noorbouharrou/CommuniMate/examples/schermen_knoppen_geluid/1.h

/* C:\Users\niels\Downloads\1.wav (03/02/2025 16:15:37)
   StartOffset(h): 00000000, EndOffset(h): 00001715, Length(h): 00001716 */

unsigned char rawData1[5910] PROGMEM = {
	0x52, 0x49, 0x46, 0x46, 0x0E, 0x17, 0x00, 0x00, 0x57, 0x41, 0x56, 0x45,
	0x66, 0x6D, 0x74, 0x20, 0x10, 0x00, 0x00, 0x00, 0x01, 0x00, 0x01, 0x00,
	0x40, 0x1F, 0x00, 0x00, 0x40, 0x1F, 0x00, 0x00, 0x01, 0x00, 0x08, 0x00,
	0x64, 0x61, 0x74, 0x61, 0x80, 0x16, 0x00, 0x00, 0x80, 0x80, 0x80, 0x80,
	0x80, 0x7F, 0x80, 0x7F, 0x80, 0x80, 0x80, 0x7F, 0x80, 0x7F, 0x80, 0x80,
	0x7F, 0x80, 0x80, 0x80, 0x80, 0x80, 0x7F, 0x80, 0x7F, 0x80, 0x7F, 0x80,
	0x7F, 0x80, 0x7F, 0x80, 0x7F, 0x7F, 0x80, 0x7F, 0x80, 0x7F, 0x80, 0x80,
	0x80, 0x7F, 0x80, 0x7F, 0x80, 0x7F, 0x80, 0x80, 0x7F, 0x80, 0x7F, 0x80,
	0x7F, 0x80, 0x80, 0x7F, 0x80, 0x7F, 0x80, 0x7F, 0x80, 0x7F, 0x80, 0x7F,
	0x80, 0x80, 0x7F, 0x80, 0x7F, 0x80, 0x80, 0x80, 0x7F, 0x80, 0x7F, 0x80,
	0x7F, 0x80, 0x7F, 0x80, 0x80, 0x7F, 0x80, 0x7F, 0x80, 0x80, 0x7F, 0x80,
	0x7F, 0x80, 0x7F, 0x80, 0x80, 0x7F, 0x80, 0x7F, 0x80, 0x7F, 0x80, 0x7F,
	0x80, 0x80, 0x7F, 0x80, 0x7F, 0x80, 0x7F, 0x80, 0x7F, 0x80, 0x80, 0x7F,
	0x80, 0x7F, 0x80, 0x80, 0x7F, 0x80, 0x7F, 0x80, 0x7F, 0x80, 0x7F, 0x80,
	0x7F, 0x80, 0x80, 0x7F, 0x80, 0x7F, 0x80, 0x7F, 0x80, 0x7F, 0x80, 0x80,
	0x7F, 0x80, 0x80, 0x80, 0x7F, 0x80, 0x7F, 0x80, 0x80, 0x80, 0x7F, 0x80,
	0x7F, 0x80, 0x7F, 0x80, 0x7F, 0x80, 0x80, 0x80, 0x7F, 0x80, 0x80, 0x7F,
	0x80, 0x7F, 0x80, 0x7F, 0x80, 0x7F, 0x80, 0x80, 0x80, 0x80, 0x80, 0x80,
	0x7F, 0x80, 0x7F, 0x80, 0x7F, 0x7F, 0x80, 0x7F, 0x80, 0x7F, 0x80, 0x7F,
	0x80, 0x80, 0x7F, 0x80, 0x7F, 0x7F, 0x80, 0x7F, 0x80, 0x80, 0x7F, 0x80,
	0x7F, 0x80, 0x7F, 0x80, 0x80, 0x7F, 0x80, 0x7F, 0x80, 0x7F, 0x80, 0x7F,
	0x80, 0x7F, 0x80, 0x7F, 0x80, 0x7F, 0x80, 0x7F, 0x80, 0x7F, 0x7F, 0x80,
	0x7F, 0x80, 0x80, 0x7F, 0x80, 0x7F, 0x80, 0x7F, 0x80, 0x80, 0x80, 0x80,
	0x80, 0x80, 0x80, 0x80, 0x80, 0x7F, 0x80, 0x7F, 0x80, 0x7F, 0x80, 0x7F,
	0x80, 0x7F, 0x80, 0x80, 0x7F, 0x80, 0x7F, 0x80, 0x7F, 0x80, 0x7F, 0x80,
	0x7F, 0x80, 0x7F, 0x80, 0x7F, 0x80, 0x7F, 0x80, 0x80, 0x7F, 0x80, 0x7F,
	0x80, 0x7F, 0x80, 0x7F, 0x80, 0x80, 0x7F, 0x80, 0x7F, 0x80, 0x7F, 0x80,
	0x80, 0x7F, 0x80, 0x7F, 0x80, 0x80, 0x80, 0x7F, 0x80, 0x80, 0x7F, 0x80,
	0x7F, 0x80, 0x7F, 0x80, 0x80, 0x7F, 0x80, 0x80, 0x7F, 0x80, 0x7F, 0x80,
	0x7F, 0x80, 0x7F, 0x80, 0x7F, 0x80, 0x7F, 0x80, 0x7F, 0x80, 0x7F, 0x80,
	0x7F, 0x80, 0x7F, 0x80, 0x7F, 0x80, 0x80, 0x7F, 0x80, 0x80, 0x7F, 0x80,
	0x7F, 0x80, 0x80, 0x7F, 0x80, 0x7F, 0x80, 0x80, 0x7F, 0x80, 0x80, 0x7F,
	0x80, 0x80, 0x7F, 0x80, 0x7F, 0x80, 0x7F, 0x80, 0x7F, 0x80, 0x7F, 0x80,
	0x7F, 0x80, 0x7F, 0x80, 0x7F, 0x80, 0x80, 0x7F, 0x80, 0x80, 0x7F, 0x80,
	0x7F, 0x7F, 0x80, 0x7F, 0x80, 0x7F, 0x80, 0x80, 0x80, 0x80, 0x80, 0x80,
	0x80, 0x80, 0x7F, 0x80, 0x80, 0x7F, 0x80, 0x80, 0x7F, 0x80, 0x7F, 0x80,
	0x7F, 0x80, 0x80, 0x7F, 0x80, 0x7F, 0x80, 0x7F, 0x7F, 0x80, 0x80, 0x7F,
	0x80, 0x7F, 0x80, 0x80, 0x7F, 0x80, 0x80, 0x7F, 0x80, 0x7F, 0x80, 0x7F,
	0x80, 0x7F, 0x80, 0x7F, 0x80, 0x80, 0x7F, 0x80, 0x80, 0x7F, 0x80, 0x7F,
	0x80, 0x80, 0x80, 0x7F, 0x80, 0x7F, 0x80, 0x80, 0x7F, 0x80, 0x7F, 0x80,
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
};
