noorbouharrou/CommuniMate/examples/schermen_knoppen_geluid/image1.h

// array size is 21649
static const unsigned char image1[] PROGMEM  = {
  0x89, 0x50, 0x4e, 0x47, 0x0d, 0x0a, 0x1a, 0x0a, 0x00, 0x00, 0x00, 0x0d, 0x49, 0x48, 0x44, 0x52, 
  0x00, 0x00, 0x00, 0xf0, 0x00, 0x00, 0x00, 0xf0, 0x08, 0x06, 0x00, 0x00, 0x00, 0x3e, 0x55, 0xe9, 
  0x92, 0x00, 0x00, 0x00, 0x09, 0x70, 0x48, 0x59, 0x73, 0x00, 0x00, 0x0e, 0xc3, 0x00, 0x00, 0x0e, 
  0xc3, 0x01, 0xc7, 0x6f, 0xa8, 0x64, 0x00, 0x00, 0x01, 0xc5, 0x74, 0x45, 0x58, 0x74, 0x52, 0x61, 
  0x77, 0x00, 0x0a, 0x65, 0x78, 0x69, 0x66, 0x0a, 0x20, 0x20, 0x20, 0x20, 0x20, 0x32, 0x31, 0x34, 
  0x0a, 0x34, 0x35, 0x37, 0x38, 0x36, 0x39, 0x36, 0x36, 0x30, 0x30, 0x30, 0x30, 0x34, 0x39, 0x34, 
  0x39, 0x32, 0x61, 0x30, 0x30, 0x30, 0x38, 0x30, 0x30, 0x30, 0x30, 0x30, 0x30, 0x30, 0x61, 0x30, 
  0x30, 0x30, 0x30, 0x30, 0x31, 0x30, 0x34, 0x30, 0x30, 0x30, 0x31, 0x30, 0x30, 0x30, 0x30, 0x30, 
  0x30, 0x30, 0x30, 0x30, 0x32, 0x30, 0x30, 0x30, 0x30, 0x30, 0x31, 0x30, 0x31, 0x30, 0x34, 0x30, 
  0x30, 0x30, 0x31, 0x30, 0x30, 0x30, 0x30, 0x30, 0x30, 0x0a, 0x30, 0x30, 0x30, 0x32, 0x30, 0x30, 
  0x30, 0x30, 0x30, 0x32, 0x30, 0x31, 0x30, 0x33, 0x30, 0x30, 0x30, 0x33, 0x30, 0x30, 0x30, 0x30, 
  0x30, 0x30, 0x38, 0x36, 0x30, 0x30, 0x30, 0x30, 0x30, 0x30, 0x31, 0x32, 0x30, 0x31, 0x30, 0x33, 
  0x30, 0x30, 0x30, 0x31, 0x30, 0x30, 0x30, 0x30, 0x30, 0x30, 0x30, 0x31, 0x30, 0x30, 0x30, 0x30, 
  0x30, 0x30, 0x31, 0x61, 0x30, 0x31, 0x30, 0x35, 0x30, 0x30, 0x30, 0x31, 0x30, 0x30, 0x30, 0x30, 
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
  0xee, 0x3b, 0xdf, 0xad, 0xfa, 0x5b, 0xdd, 0x52, 0x55, 0x75, 0x4b, 0x6a, 0xa9, 0x53, 0xf5, 0x39, 
  0xf7, 0x08, 0xa4, 0xee, 0xea, 0x0a, 0xff, 0xf7, 0xdf, 0xef, 0x66, 0x43, 0xd5, 0xde, 0x1a, 0xd2, 
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
};
